petercampellone95/MetroMiniBatteryShield/Board Images-Renders/3D_View_Bottom.PNG

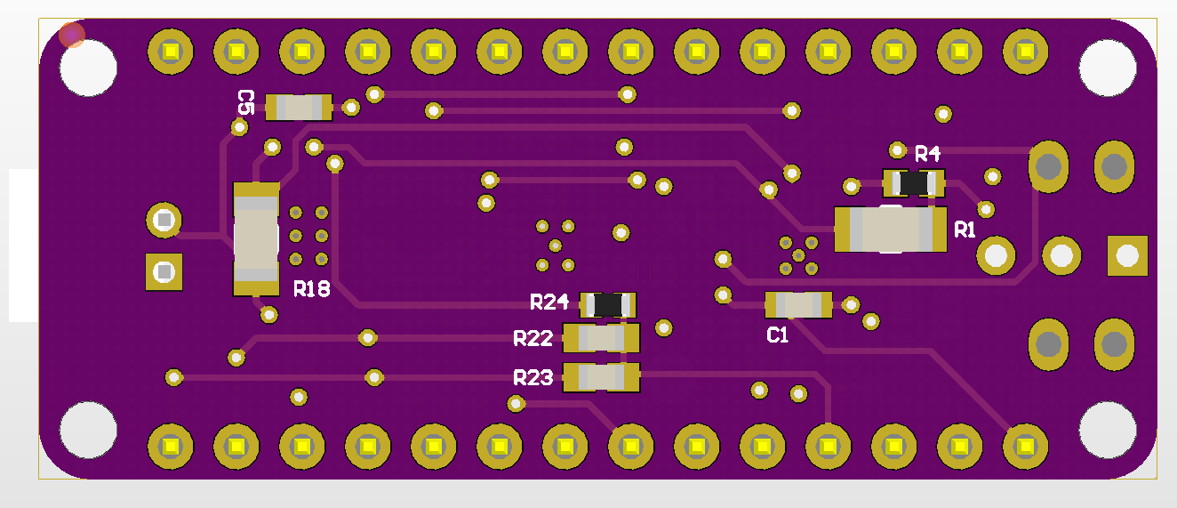
Board Images-Renders/3D_View_Bottom.PNG
