petercampellone95/MetroMiniBatteryShield/Board Images-Renders/3D_View_Front.PNG

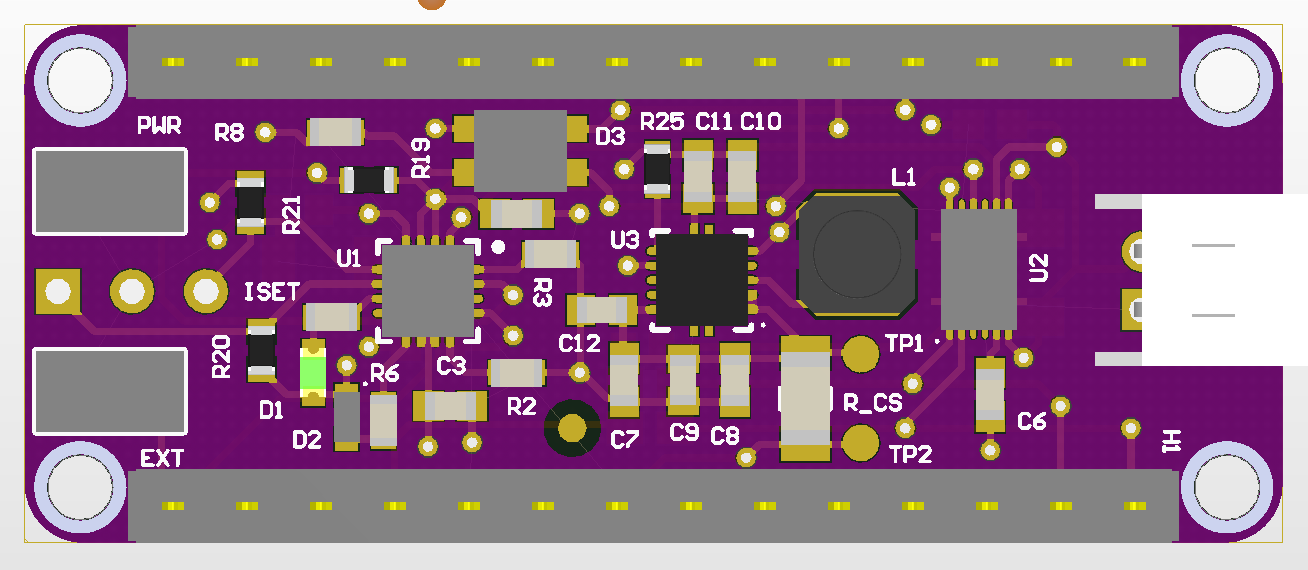
Board Images-Renders/3D_View_Front.PNG
