petercampellone95/MetroMiniBatteryShield/Board Images-Renders/BottomLayer.PNG

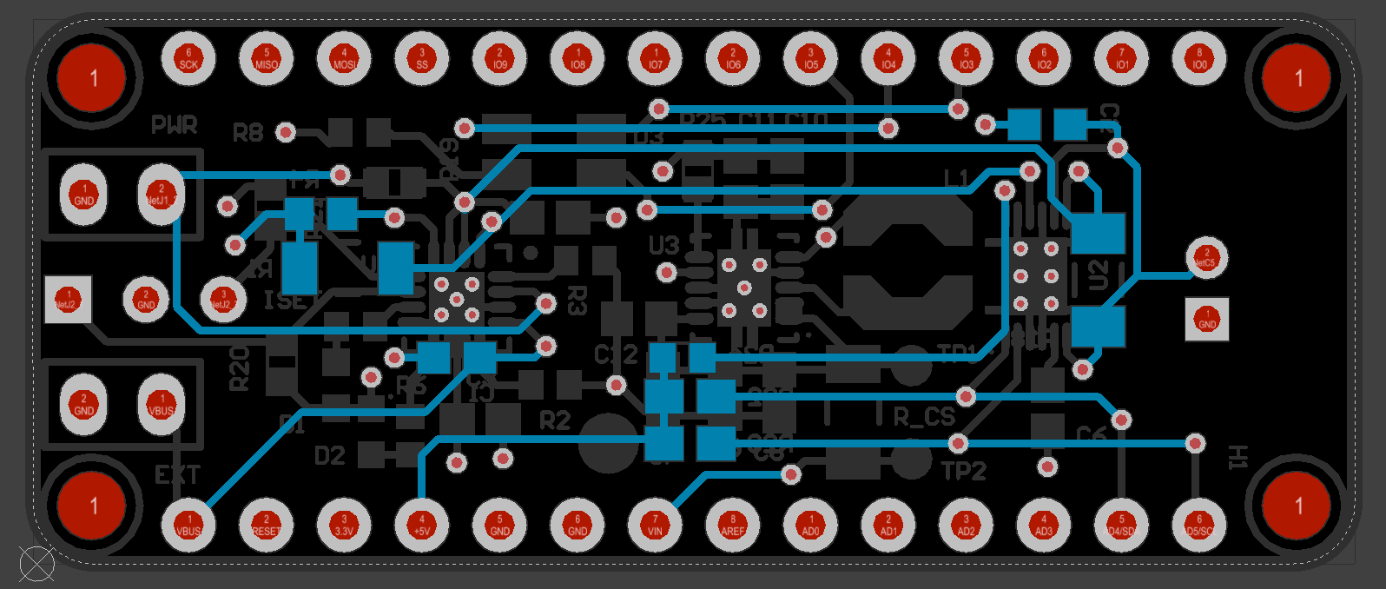
Board Images-Renders/BottomLayer.PNG
