petercampellone95/MetroMiniBatteryShield/Board Images-Renders/TopLayer.PNG

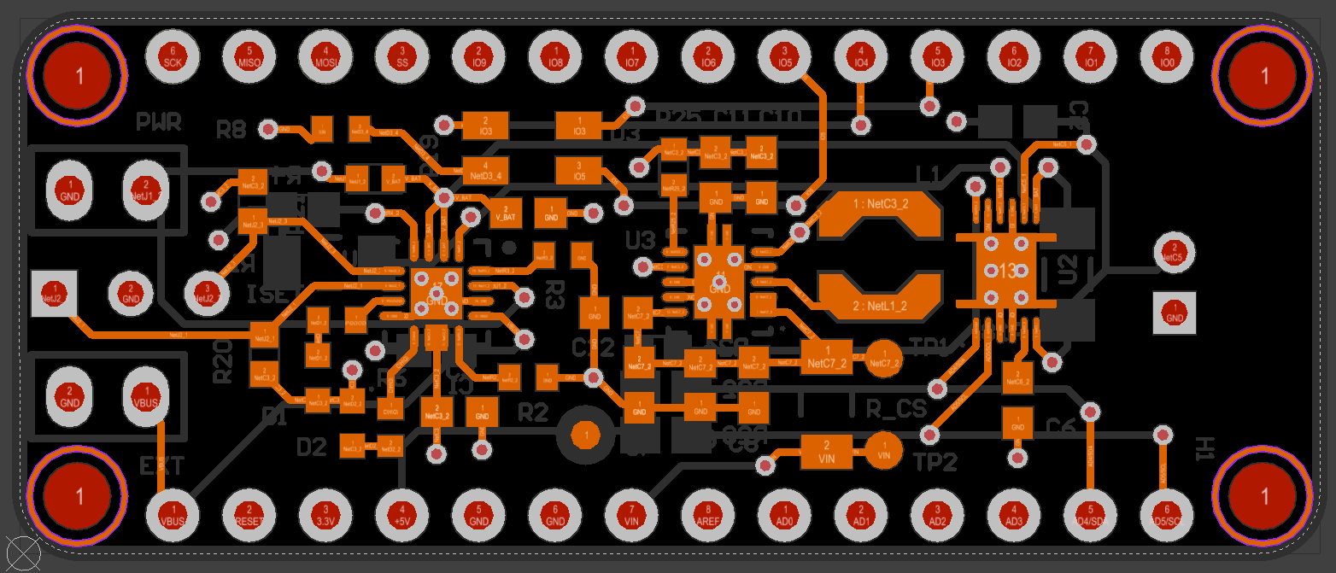
Board Images-Renders/TopLayer.PNG
